esar/hdmilight-v3/firmware/ambilight.h

/*

   Copyright (C) 2013 Stephen Robinson
  
   This file is part of HDMI-Light
  
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
*/

#define BELL    '\a'


#define AMBILIGHT_BASE_ADDR_OUTPUT 0x0000
#define AMBILIGHT_BASE_ADDR_COLOUR 0x2000
#define AMBILIGHT_BASE_ADDR_AREA   0x3000
#define AMBILIGHT_BASE_ADDR_GAMMAR 0x4000
#define AMBILIGHT_BASE_ADDR_GAMMAG 0x4800
#define AMBILIGHT_BASE_ADDR_GAMMAB 0x5000
#define AMBILIGHT_BASE_ADDR_RESULT 0x5800
#define AMBILIGHT_BASE_ADDR_STATUS 0x6000
#define AMBILIGHT_BASE_ADDR_DELAY  0x6800
#define AMBILIGHT_BASE_ADDR_FORMAT 0x7000
#define AMBILIGHT_BASE_ADDR_INTERRUPT 0x7800

#define AMBILIGHT_FLASH_CONFIG_OFFSET 0x60000

#define ACTION_NONE           0
#define ACTION_POWER_TOGGLE    1
#define ACTION_CONFIG_AUTO     2
#define ACTION_CONFIG_0        3
#define ACTION_CONFIG_1        4
#define ACTION_CONFIG_2        5
#define ACTION_CONFIG_3        6
#define ACTION_CONFIG_4        7
#define ACTION_CONFIG_5        8
#define ACTION_CONFIG_6        9
#define ACTION_CONFIG_7        10
#define ACTION_CONFIG_8        11
#define ACTION_CONFIG_CYCLE    12
#define ACTION_ADJUST_CYCLE    13
#define ACTION_ADJUST_UP       14
#define ACTION_ADJUST_DOWN     15
#define ACTION_ADJUST_BRIGHTNESS 16
#define ACTION_ADJUST_CONTRAST   17
#define ACTION_ADJUST_SATURATION 18
#define ACTION_ADJUST_HUE        19

#define INT_PRIORITY_DEVICE_COMMS    4    /* IRQs that communicate with FPGA or ADV7611 */


extern uint8_t silent;
extern volatile uint8_t g_formatChanged;
extern volatile uint8_t g_cecMessage[16];
extern volatile uint8_t g_cecMessageLength;


char readcmd(char** argv, char maxargs);
int getint(char** str);
void getrange(char* str, uint8_t* min, uint8_t* max);

uint32_t getfixed_9_9(const char* p);
int fixed_9_9_fract(int32_t x, int numDigits);
int fixed_9_9_int(int32_t x);

void suspend();
void resume();

void clockInit();
uint32_t clockGetTicks();

void powerInit();
void powerLEDOff();
void powerLEDOn();
void power1V8Off();
void power1V8On();
void power1V2Off();
void power1V2On();

void standbyInit();
void standbyPoll();

void adv7611Init();
void adv7611Suspend();
void adv7611Resume();
uint8_t adv7611ReadRegister(uint8_t addr, uint8_t subaddr);
uint8_t adv7611WriteRegister(uint8_t addr, uint8_t subaddr, uint8_t value);

void fpgaInit();
void fpgaSuspend();
void fpgaResume();
void fpgaConfigWrite(uint16_t address, void* data, uint16_t length);
void fpgaConfigRead(uint16_t address, void* data, uint16_t length);
void fpgaConfigLoad(uint8_t slot);
uint8_t fpgaConfigStatus();
void fpgaFlashRead(uint32_t address, void* data, int length);
void fpgaFlashWrite(uint32_t address, void* data, int length);

void formatInit();
void formatSuspend();
void formatResume();
void formatChange();
void formatEnable(int enable);
void formatGetCurrent(uint16_t* currentWidth, uint16_t* currentHeight, uint16_t* currentRatio);
char* formatGetRatioName(uint16_t ratio);

void processCecMessage();

void cmdGetArea(uint8_t argc, char** argv);
void cmdSetArea(uint8_t argc, char** argv);
void cmdRstArea(uint8_t argc, char** argv);

void cmdGetAddr(uint8_t argc, char** argv);
void cmdSetAddr(uint8_t argc, char** argv);

void cmdGetColour(uint8_t argc, char** argv);
void cmdSetColour(uint8_t argc, char** argv);
void cmdRstColour(uint8_t argc, char** argv);

void cmdGetDelay(uint8_t argc, char** argv);
void cmdSetDelay(uint8_t argc, char** argv);
void cmdRstDelay(uint8_t argc, char** argv);

void cmdGetGamma(uint8_t argc, char** argv);
void cmdSetGamma(uint8_t argc, char** argv);
void cmdRstGamma(uint8_t argc, char** argv);

void cmdGetI2C(uint8_t argc, char** argv);
void cmdSetI2C(uint8_t argc, char** argv);
void cmdRstI2C(uint8_t argc, char** argv);

void cmdSetKeys(uint8_t argc, char** argv);
void cmdRstKeys(uint8_t argc, char** argv);

void cmdGetMem(uint8_t argc, char** argv);

void cmdGetOutput(uint8_t argc, char** argv);
void cmdSetOutput(uint8_t argc, char** argv);
void cmdRstOutput(uint8_t argc, char** argv);

void cmdGetPort(uint8_t argc, char** argv);
void cmdSetPort(uint8_t argc, char** argv);

void cmdGetResult(uint8_t argc, char** argv);

void cmdGetStatus(uint8_t argc, char** argv);
void cmdSetStatus(uint8_t argc, char** argv);

void cmdDisFormat(uint8_t argc, char** argv);
void cmdEnaFormat(uint8_t argc, char** argv);
void cmdGetFormat(uint8_t argc, char** argv);

void cmdGetStack(uint8_t argc, char** argv);
