esar/hdmilight-v3/firmware/cmd_colour.c

/*

   Copyright (C) 2013 Stephen Robinson
  
   This file is part of HDMI-Light
  
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
*/

#include <stdint.h>
#include <string.h>
#include "printf.h"
#include "ambilight.h"


void setColour(uint8_t index, uint8_t row, uint32_t r, uint32_t g, uint32_t b)
{
	uint16_t address = AMBILIGHT_BASE_ADDR_COLOUR;
	address += (uint16_t)index * 32;
	address += row * 8;

	//       54                45                36                27                18                 9                 0
	// +-/\+-+-+-+-+-+-+-+-+-+-+-+-+-+-+-+-+-+-+-+-+-+-+-+-+-+-+-+-+-+-+-+-+-+-+-+-+-+-+-+-+-+-+-+-+-+-+-+-+-+-+-+-+-+-+-+-+
	// |       | Bint            | Bfract          | Gint            | Gfract          | Rint            | Rfract          |
	// +-\/+-+-+-+-+-+-+-+-+-+-+-+-+-+-+-+-+-+-+-+-+-+-+-+-+-+-+-+-+-+-+-+-+-+-+-+-+-+-+-+-+-+-+-+-+-+-+-+-+-+-+-+-+-+-+-+-+
	// |   |   byte 6      |    byte 5     |    byte 4     |    byte 3     |    byte 2     |    byte 1     |    byte 0     |

	uint8_t data[8] = {0, 0, 0, 0, 0, 0, 0, 0};
	uint32_t* rdata = (uint32_t*)data;
	uint32_t* gdata = (uint32_t*)&data[2];
	uint32_t* bdata = (uint32_t*)&data[4];
	*rdata  = (r & 0x3FFFFUL);
	*gdata |= (g & 0x3FFFFUL) << 2;
	*bdata |= (b & 0x3FFFFUL) << 4;
	
	fpgaConfigWrite(address, data, sizeof(data));
}

void getColour(uint8_t index, uint8_t row, uint32_t* r, uint32_t* g, uint32_t* b)
{
	uint16_t address = AMBILIGHT_BASE_ADDR_COLOUR;
	address += (uint16_t)index * 32;
	address += row * 8;
	
	uint8_t data[8];
	uint32_t* rdata = (uint32_t*)data;
	uint32_t* gdata = (uint32_t*)&data[2];
	uint32_t* bdata = (uint32_t*)&data[4];

	fpgaConfigRead(address, data, sizeof(data));

	*r = *rdata & 0x3FFFFUL;
	*g = (*gdata >> 2) & 0x3FFFFUL;
	*b = (*bdata >> 4) & 0x3FFFFUL;
}

void cmdSetColour(uint8_t argc, char** argv)
{
	if(argc == 6)
	{
		uint32_t r, g, b;
		uint8_t index, maxIndex;
		uint8_t row, minRow, maxRow;

		r = getfixed_9_9(argv[3]);
		g = getfixed_9_9(argv[4]);
		b = getfixed_9_9(argv[5]);
		
		getrange(argv[1], &index, &maxIndex);
		getrange(argv[2], &minRow, &maxRow);
		do
		{
			row = minRow;
			do
			{
				setColour(index, row, r, g, b);
				
			} while(row++ < maxRow);
			
		} while(index++ < maxIndex);
	}
}

void cmdGetColour(uint8_t argc, char** argv)
{
	if(argc == 3)
	{
		uint8_t index, maxIndex;
		uint8_t row, minRow, maxRow;

		getrange(argv[1], &index, &maxIndex);
		getrange(argv[2], &minRow, &maxRow);
		do
		{
			row = minRow;
			do
			{
				uint32_t r, g, b;

				getColour(index, row, &r, &g, &b);

				printf("%d %d: %d.%03d %d.%03d %d.%03d\n", index, row, 
				         fixed_9_9_int(r), fixed_9_9_fract(r, 3),
				         fixed_9_9_int(g), fixed_9_9_fract(g, 3),
				         fixed_9_9_int(b), fixed_9_9_fract(b, 3));
				
			} while(row++ < maxRow);
			
		} while(index++ < maxIndex);
	}
}

void cmdRstColour(uint8_t argc, char** argv)
{
	int i;
	for(i = 0; i < 8; ++i)
	{
		setColour(i, 0, 0x200, 0,     0);
		setColour(i, 1, 0,     0x200, 0);
		setColour(i, 2, 0,     0,     0x200);
		setColour(i, 3, 0,     0,     0);
	}
}
